sdunlap-afit/hilics/src/images/Car1.png

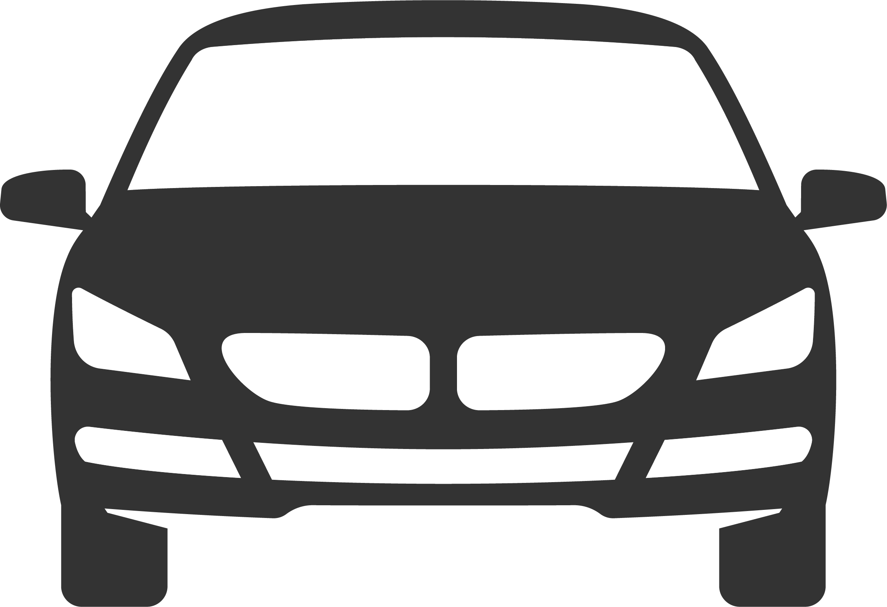
src/images/Car1.png
