sdunlap-afit/hilics/src/images/explosion.png

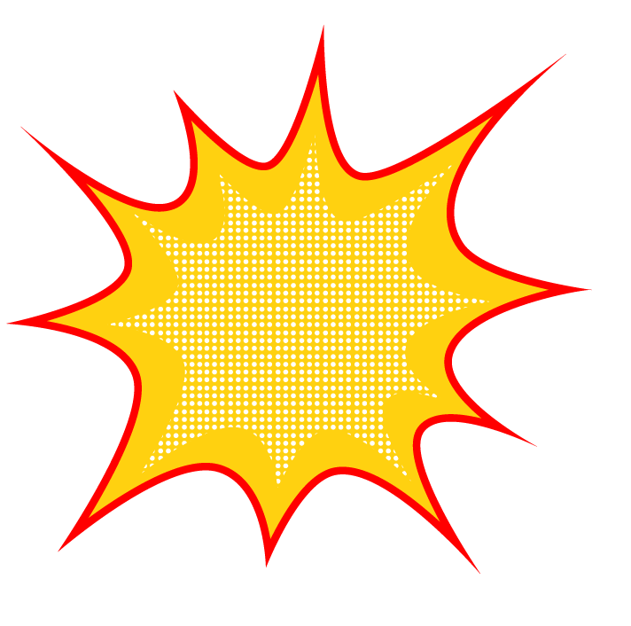
src/images/explosion.png
